fcte-pi1/2026.2_PI1_Grupo2_Hilmer/docs/1 - TAP.md

# Termo de Abertura do Projeto

## Visão Geral do Projeto

### Dados do projeto

- **Nome do Projeto: MicroMouse Grupo 2**
- **Data de Início:  02/09/2026**
- **Data de Término: 04/12/2026**
- **Patrocinador:** Universidade de Brasília

### Objetivos

Desenvolver, integrar e validar, até o término do segundo semestre letivo de 2026, um sistema micromouse autônomo capaz de navegar e concluir os três tipos de labirintos propostos (4×4, 8×4 e 12×4 células) sem intervenção humana durante a execução, identificando paredes, monitorando sua localização, mapeando o percurso e reconhecendo a chegada ao objetivo. O sistema deverá ainda disponibilizar, em tempo real, dados de telemetria por meio de uma aplicação web e armazenar os resultados obtidos em banco de dados para consultas posteriores, atendendo às restrições físicas e operacionais estabelecidas para o projeto.

### Público-Alvo

O público-alvo do projeto é composto principalmente por estudantes, professores, pesquisadores e instituições de ensino envolvidos com engenharia, robótica, automação, sistemas embarcados e áreas correlatas. O sistema desenvolvido também pode servir como plataforma didática para atividades de ensino, pesquisa e extensão relacionadas à integração de conhecimentos de estruturas, eletrônica, energia, hardware, software, controle e desenvolvimento de sistemas autônomos. De forma indireta, os resultados do projeto também podem beneficiar equipes e grupos acadêmicos envolvidos em competições e projetos de robótica móvel. 

### Descrição do Problema

O projeto surge da necessidade de desenvolver uma solução integrada de engenharia capaz de realizar navegação autônoma em ambientes previamente desconhecidos. Para cumprir a tarefa proposta, o sistema deverá identificar obstáculos e paredes, determinar sua própria localização, construir uma representação do labirinto, definir um percurso e reconhecer a chegada ao destino sem intervenção humana durante a execução. Além da navegação, existe a necessidade de monitorar o desempenho do sistema por meio da aquisição, transmissão, visualização e armazenamento de dados de telemetria. Dessa forma, o projeto propõe a integração de conhecimentos das diferentes áreas de engenharia da FCTE na concepção e validação de um sistema robótico autônomo funcional. 

### Indicadores

- 1 - Número de estudantes matriculados nos cursos de engenharia da FCTE/UnB que podem utilizar projetos de robótica como recurso de ensino;
- 2 - Número de cursos de graduação da FCTE cujos conhecimentos podem ser aplicados ao desenvolvimento do micromouse;
- 3 - Número de disciplinas da FCTE relacionadas a robótica, automação, programação, eletrônica, controle, sistemas embarcados e projeto de engenharia;
- 4 - Número de estudantes envolvidos em equipes ou projetos de robótica na universidade;
- 5 - Número de instituições de ensino superior no Distrito Federal que oferecem cursos de engenharia ou áreas relacionadas à robótica;
- 6 - Quantidade de competições acadêmicas ou estudantis relacionadas à robótica móvel e sistemas autônomos;
- 7 - Número de estudantes de engenharia e áreas tecnológicas no Distrito Federal;
- 8 - Número de laboratórios, grupos de pesquisa ou instituições acadêmicas do Distrito Federal relacionados à robótica, automação ou sistemas autônomos.

### Membros da Equipe

| NOME | MATRÍCULA | CURSO | E-MAIL | FUNÇÕES |
| :--- | :--- | :--- | :--- | :--- |
| JOÃO FELIPE VELOSO ROSA | 251010892 | AEROESPACIAL | 251010892@aluno.unb.br | Gerente de Projeto<br>Estruturas |
| LORENA REGE DE SOUSA ALVES | 251012298 | AEROESPACIAL | 251012298@aluno.unb.br | Gerente de Projeto<br>Estruturas |
| JÚLIA PÊGO DE MENESES | 231037745 | SOFTWARE | 231037745@aluno.unb.br | Energia |
| PEDRO HENRIQUE CONCEIÇÃO DE SOUZA | 232330032 | SOFTWARE | 232030032@aluno.unb.br | Energia |
| MARIA EDUARDA DANTAS | 232029229 | SOFTWARE | 232029229@aluno.unb.br | Estruturas |
| ARTUR HANDOW KRAUSPENHAR | 231034082 | SOFTWARE | 231034082@aluno.unb.br | Hardware |
| KEVIN FERREIRA NUNES DE SOUSA | 232039083 | SOFTWARE | 232039083@aluno.unb.br | Energia |
| JOÃO PEDRO DE SOUSA SILVA | 232003723 | SOFTWARE | 232003723@aluno.unb.br | Software |
| VITOR COELHO COSTA | 251016359 | SOFTWARE | 251016359@aluno.unb.br | Hardware |
| LAURA DE CARVALHO FEITOSA | 251024593 | ELETRÔNICA | 251024593@aluno.unb.br | Hardware |
| JEAN DAVID BENTO DOS SANTOS | 241025775 | AUTOMOTIVA | 241025775@aluno.unb.br | Estruturas |
| DANIEL MOURA PERES | 251035069 | SOFTWARE | 251035069@aluno.unb.br | Software |
| GABRIELLY CARVALHO DE FREITAS | 251009176 | AEROESPACIAL | 251009176@aluno.unb.br | Estruturas |
| EDUARDO HENRIQUE COUTINHO GURJÃO | 222006679 | SOFTWARE | 222006679@aluno.unb.br | Software |
| VINÍCIUS DE JESUS BESSA FERNANDES | 222006490 | SOFTWARE | 222006490@aluno.unb.br | Energia |
| FELIPE FERNANDES BRANDIM | 202016201 | SOFTWARE | 202016201@aluno.unb.br | Software |
| EDILSON RIBEIRO DA CRUZ JUNIOR | 222024461 | SOFTWARE | 222024461@aluno.unb.br | Hardware |

**Orientador: Hilmer Rodrigues Neri**

### Orçamento estimado (R$)

Para calcular o custo do projeto, baseamos-nos em projetos anteriores e exteriores à universidade e estimamos um gasto máximo de R$1275,00. Totalizando, portanto, 75 reais por integrante. 

### Duração estimada (horas)

2 aulas por semana (3,66 horas)
+
1 encontro semanal remoto (1,5 horas)
+
1 momento semanal individual (2 horas)

TOTAL:  5,33 horas por semana ⇒ 93,08 horas para o projeto
