fcte-pi1/2026.2_PI1_Grupo2_Hilmer/hw/Simulação Circuito/gráfico_simulação.png

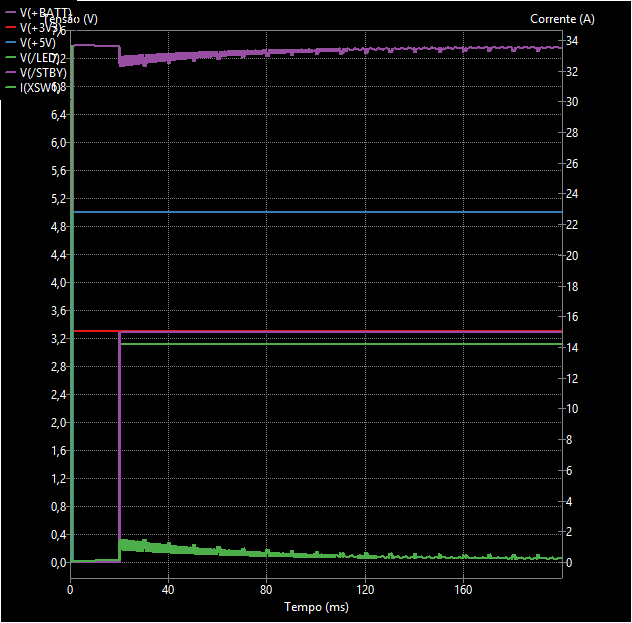
hw/Simulação Circuito/gráfico_simulação.png
