fcte-pi1/2026.2_PI1_Grupo2_Hilmer/hw/Simulação Circuito/MICROMOUSE_HARDWARE_SIM.kicad_sch

## KiCad design hw/Simulação Circuito/MICROMOUSE_HARDWARE_SIM.kicad_sch (2026-10-05)

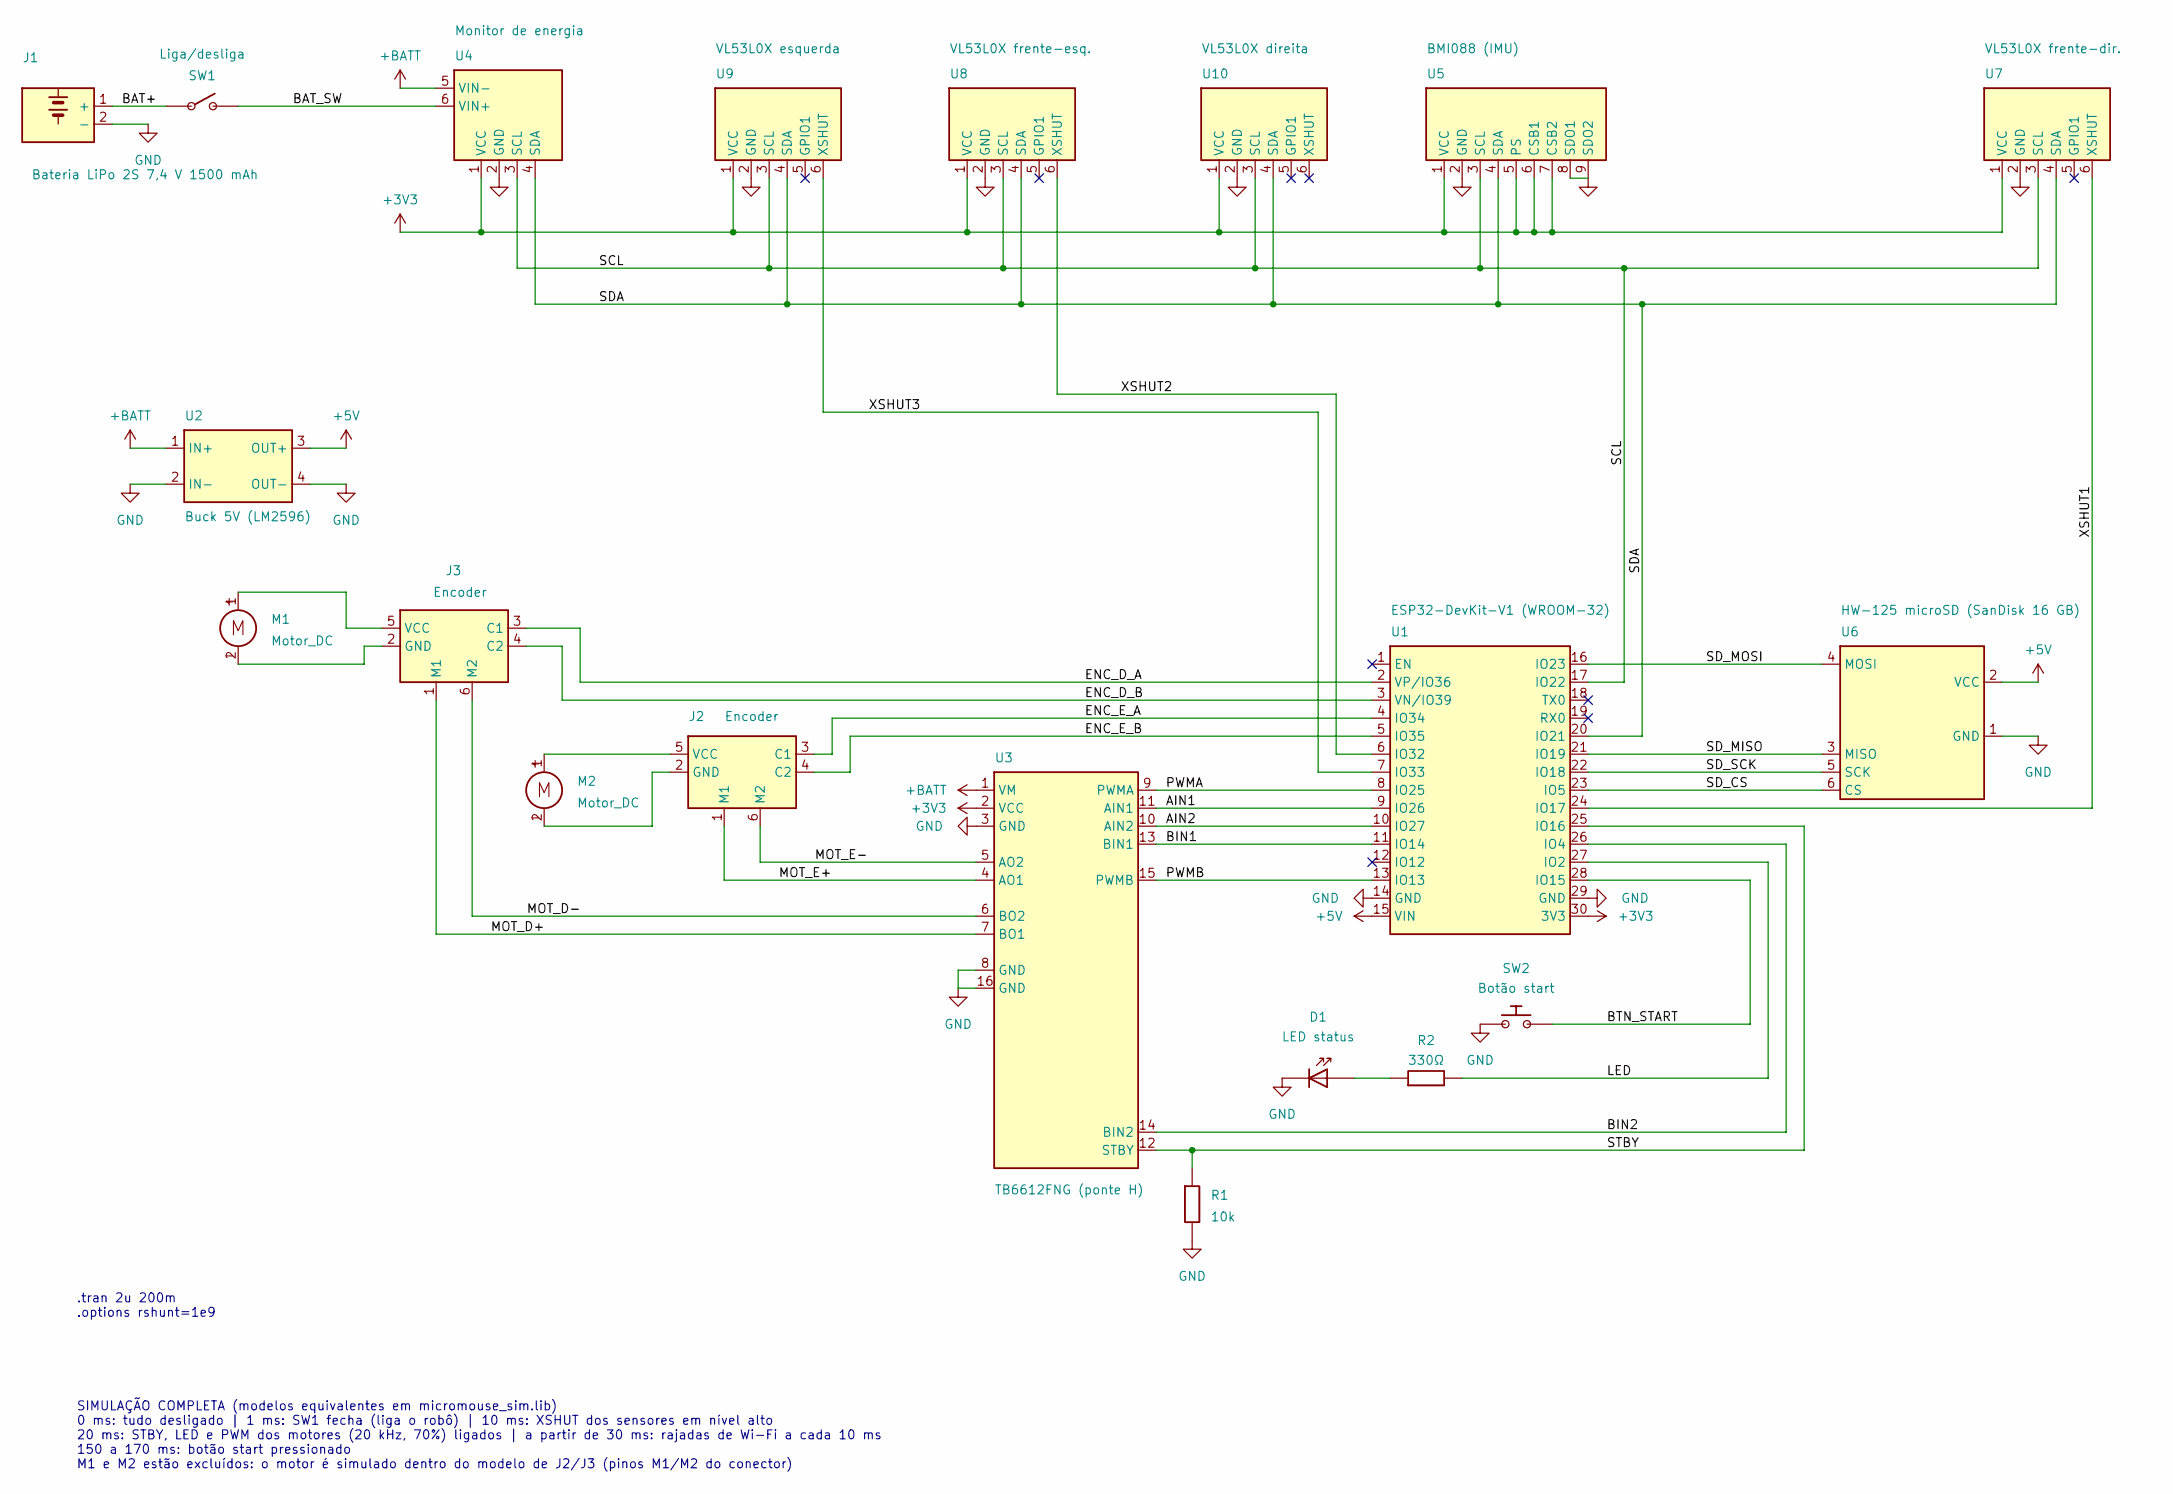
[picture p27: schematic MICROMOUSE_HARDWARE_SIM.kicad_sch]

Parts:
D1: LED status
J1: Bateria LiPo 2S 7,4 V 1500 mAh
J2, J3: Encoder
M1, M2: Motor_DC
R1: 10k
R2: 330Ω
SW1: Liga/desliga
SW2: Botão start
U1: ESP32-DevKit-V1 (WROOM-32)
U2: Buck 5V (LM2596)
U3: TB6612FNG (ponte H)
U4: Monitor de energia
U5: BMI088 (IMU)
U6: HW-125 microSD (SanDisk 16 GB)
U7: VL53L0X frente-dir.
U8: VL53L0X frente-esq.
U9: VL53L0X esquerda
U10: VL53L0X direita

Connections:
+3V3: U1.30 (3V3), U3.2 (VCC), U4.1 (VCC), U5.1 (VCC), U5.5 (PS), U5.6 (CSB1), U5.7 (CSB2), U7.1 (VCC), U8.1 (VCC), U9.1 (VCC), U10.1 (VCC)
+5V: U1.15 (VIN), U2.3 (OUT+), U6.2 (VCC)
+BATT: U2.1 (IN+), U3.1 (VM), U4.5 (VIN−)
AIN1: U1.9 (IO26), U3.11 (AIN1)
AIN2: U1.10 (IO27), U3.10 (AIN2)
BAT+: J1.1 (+), SW1.1
BAT_SW: SW1.2, U4.6 (VIN+)
BIN1: U1.11 (IO14), U3.13 (BIN1)
BIN2: U1.26 (IO4), U3.14 (BIN2)
BTN_START: SW2.2, U1.28 (IO15)
ENC_D_A: J3.3 (C1), U1.2 (VP/IO36)
ENC_D_B: J3.4 (C2), U1.3 (VN/IO39)
ENC_E_A: J2.3 (C1), U1.4 (IO34)
ENC_E_B: J2.4 (C2), U1.5 (IO35)
GND: D1.1 (K), J1.2 (−), R1.2, SW2.1, U1.14 (GND), U1.29 (GND), U2.2 (IN−), U2.4 (OUT−), U3.3 (GND), U3.8 (GND), U3.16 (GND), U4.2 (GND), U5.2 (GND), U5.8 (SDO1), U5.9 (SDO2), U6.1 (GND), U7.2 (GND), U8.2 (GND), U9.2 (GND), U10.2 (GND)
LED: R2.2, U1.27 (IO2)
MOT_D+: J3.1 (M1), U3.7 (BO1)
MOT_D-: J3.6 (M2), U3.6 (BO2)
MOT_E+: J2.1 (M1), U3.4 (AO1)
MOT_E-: J2.6 (M2), U3.5 (AO2)
unnamed: D1.2 (A), R2.1
unnamed: J2.2 (GND), M2.2 (−)
unnamed: J2.5 (VCC), M2.1 (+)
unnamed: J3.2 (GND), M1.2 (−)
unnamed: J3.5 (VCC), M1.1 (+)
PWMA: U1.8 (IO25), U3.9 (PWMA)
PWMB: U1.13 (IO13), U3.15 (PWMB)
SCL: U1.17 (IO22), U4.3 (SCL), U5.3 (SCL), U7.3 (SCL), U8.3 (SCL), U9.3 (SCL), U10.3 (SCL)
SDA: U1.20 (IO21), U4.4 (SDA), U5.4 (SDA), U7.4 (SDA), U8.4 (SDA), U9.4 (SDA), U10.4 (SDA)
SD_CS: U1.23 (IO5), U6.6 (CS)
SD_MISO: U1.21 (IO19), U6.3 (MISO)
SD_MOSI: U1.16 (IO23), U6.4 (MOSI)
SD_SCK: U1.22 (IO18), U6.5 (SCK)
STBY: R1.1, U1.25 (IO16), U3.12 (STBY)
XSHUT1: U1.24 (IO17), U7.6 (XSHUT)
XSHUT2: U1.6 (IO32), U8.6 (XSHUT)
XSHUT3: U1.7 (IO33), U9.6 (XSHUT)

Notes on the sheet:
.tran 2u 200m .options rshunt=1e9
SIMULAÇÃO COMPLETA (modelos equivalentes em micromouse_sim.lib) 0 ms: tudo desligado | 1 ms: SW1 fecha (liga o robô) | 10 ms: XSHUT dos sensores em nível alto 20 ms: STBY, LED e PWM dos motores (20 kHz, 70%) ligados | a partir de 30 ms: rajadas de Wi-Fi a cada 10 ms 150 a 170 ms: botão start pressi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
